wb1016/blueslime-files/r2-1021/3dpreview.png

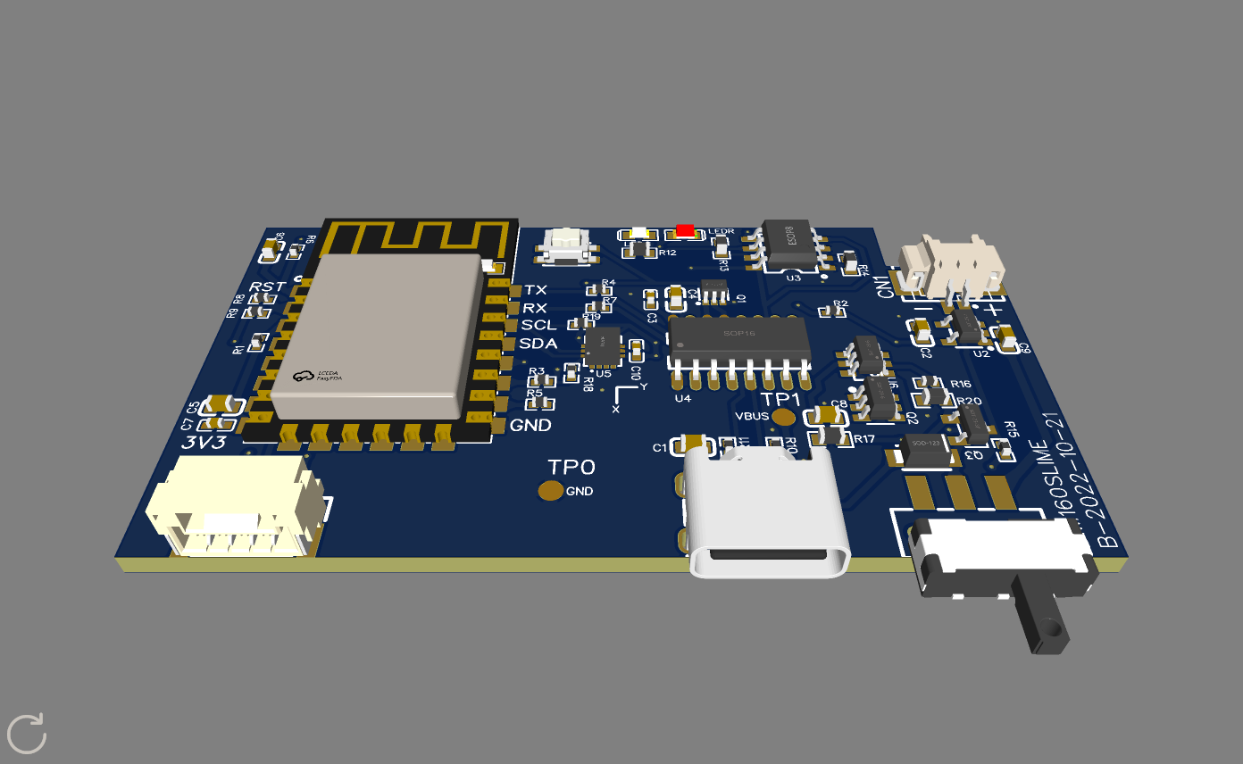
r2-1021/3dpreview.png
