wb1016/blueslime-files/r4-0216/pcbpreview.png

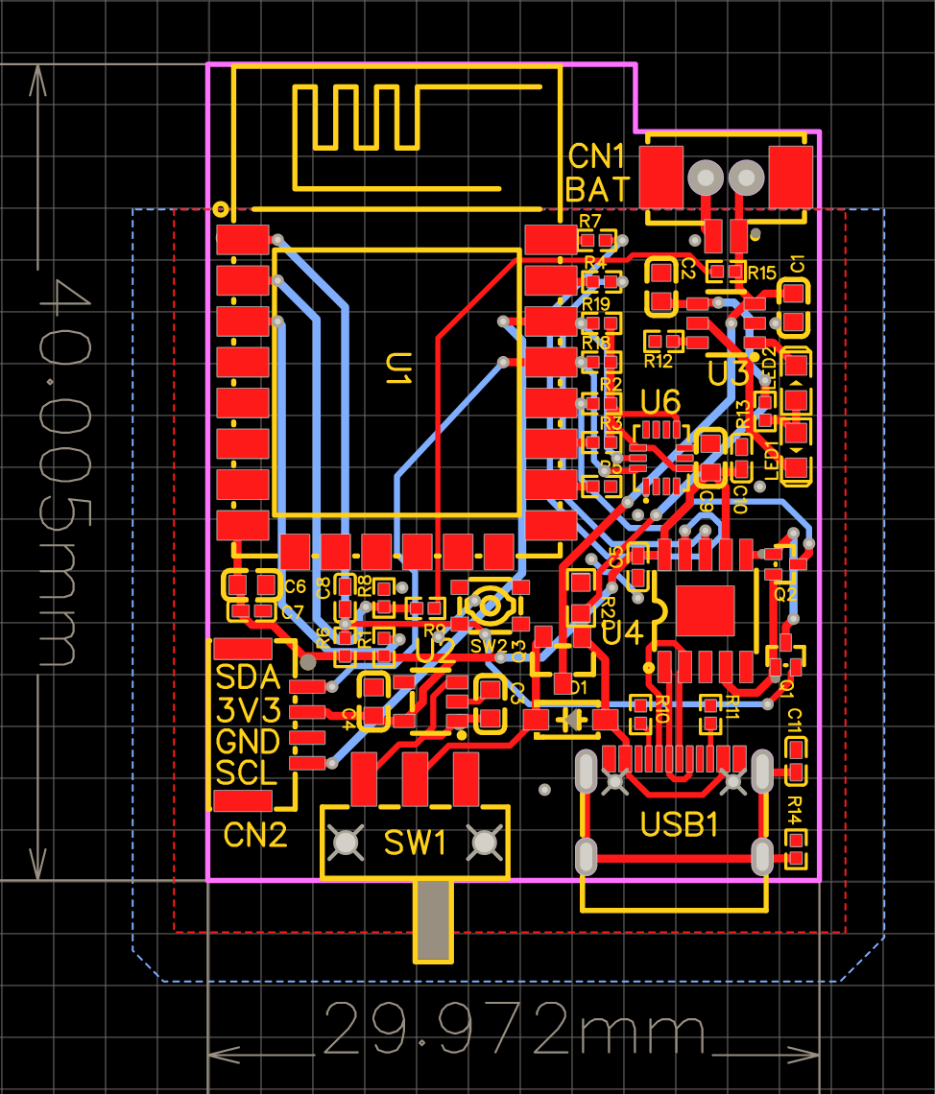
r4-0216/pcbpreview.png
