wb1016/blueslime-files/r5-0904/OBJ_PCB-r5.3mf

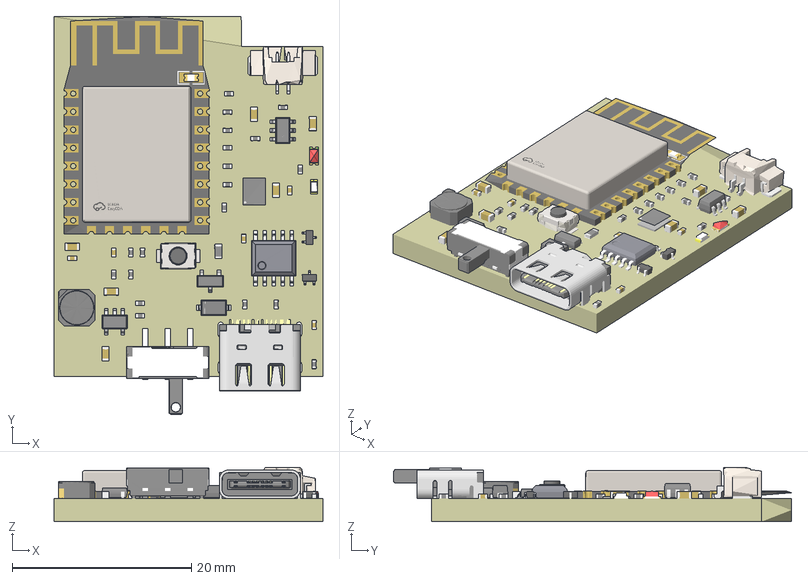
[picture p23: CAD file, 2023-09-11]
r5-0904/OBJ_PCB-r5.3mf
30.0 x 44.4 x 6.05 mm
