wb1016/blueslime-files/r4-0216/103040-case-main.stl

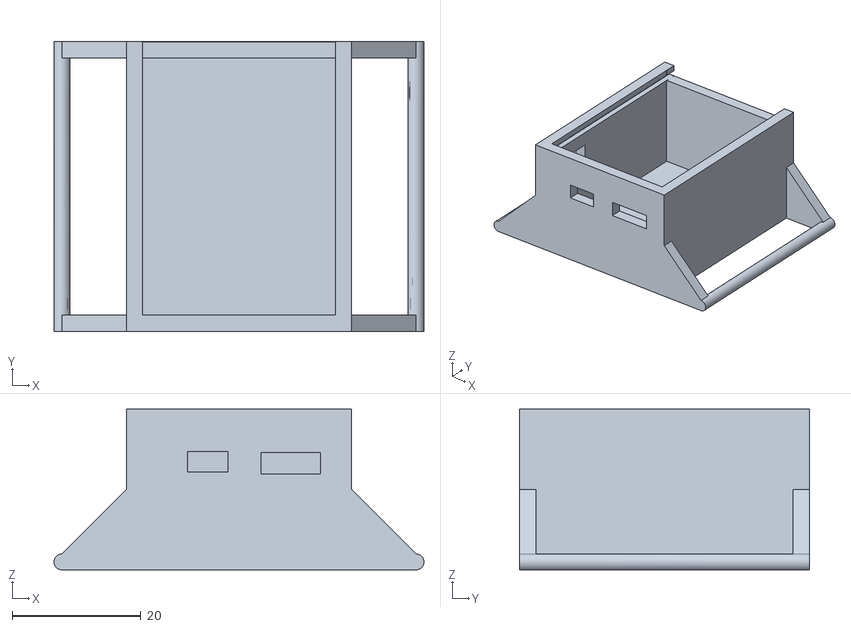
[picture p24: CAD file, 2023-03-06]
r4-0216/103040-case-main.stl
57.5 x 45.0 x 25.0
