wb1016/blueslime-files/r4-0216/804040-lid.stl

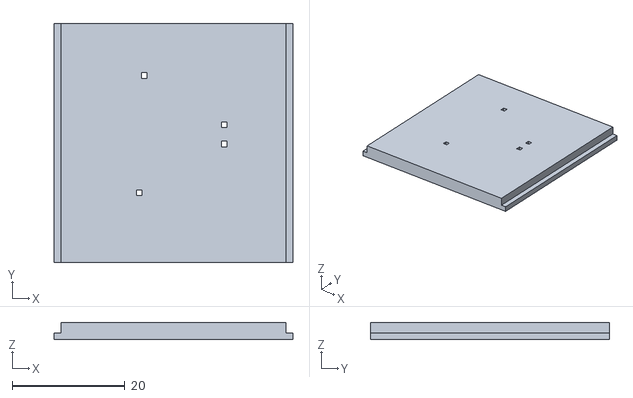
[picture p25: CAD file, 2023-06-26]
r4-0216/804040-lid.stl
42.5 x 42.5 x 3.11
