wb1016/blueslime-files/r4-0216/103040-case-lid.stl

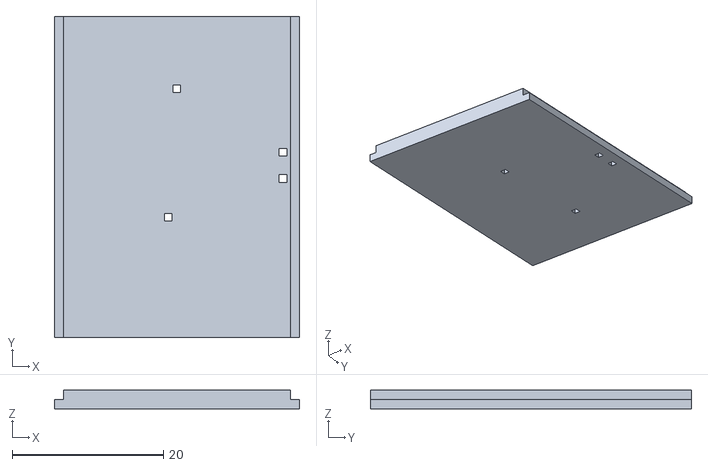
[picture p26: CAD file, 2023-06-26]
r4-0216/103040-case-lid.stl
32.5 x 42.5 x 2.50
